noahhaworth/harry/src/champ/champ_description/meshes/arm/upper_arm.stl

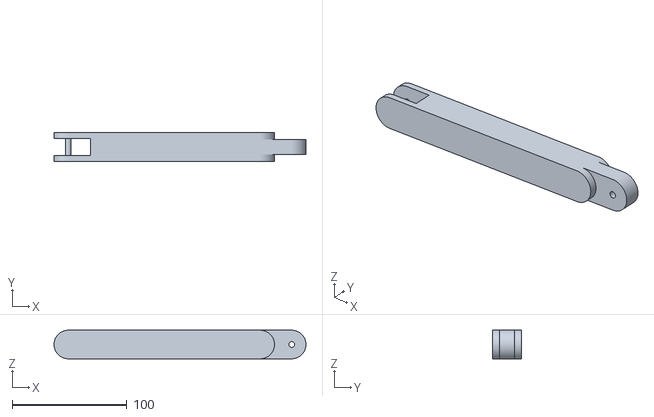
[picture p53: CAD file, 2022-01-09]
src/champ/champ_description/meshes/arm/upper_arm.stl
220.0 x 25.0 x 25.0
