noahhaworth/harry/src/champ/champ_description/meshes/base.stl

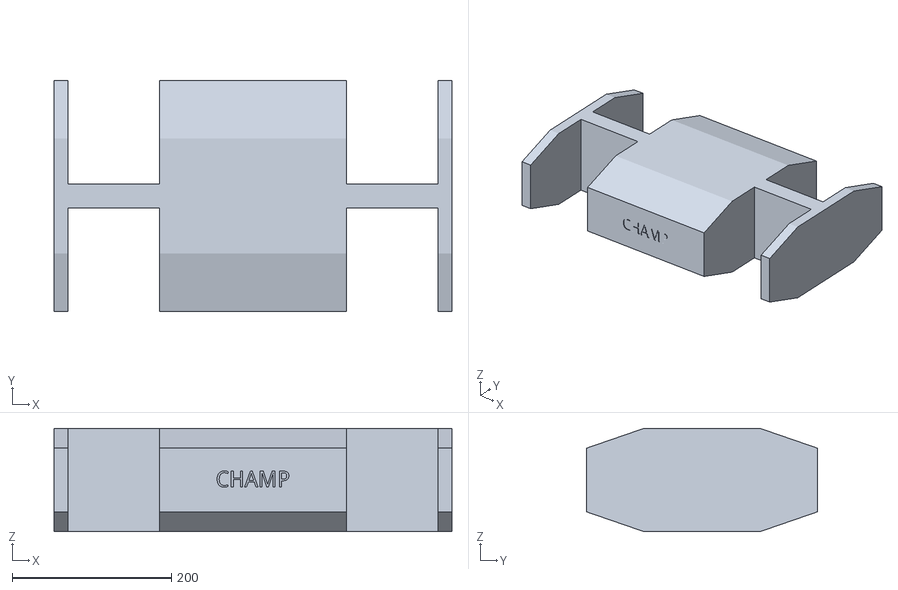
[picture p54: CAD file, 2022-01-09]
src/champ/champ_description/meshes/base.stl
500.0 x 290.0 x 130.0
