noahhaworth/harry/SolidWorks/servo.SLDPRT

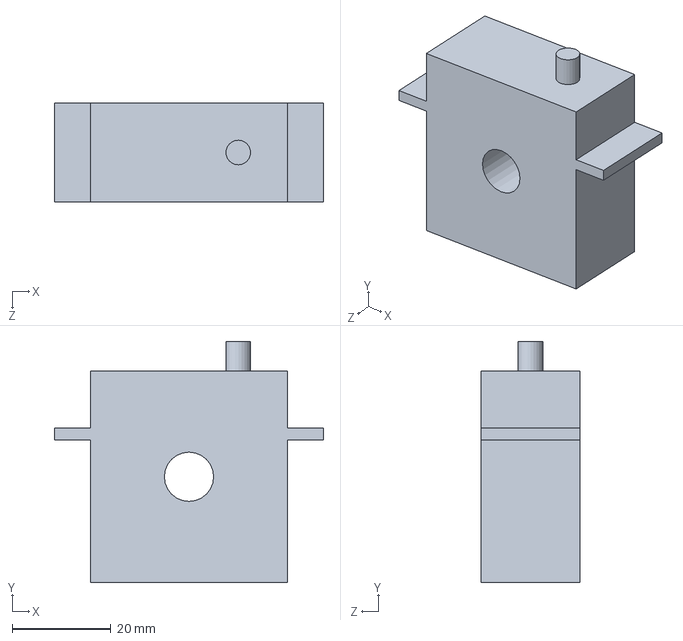
[picture p55: CAD file, 2022-05-04]
SolidWorks/servo.SLDPRT
54.6 x 49.0 x 20.0 mm
