noahhaworth/harry/src/champ/champ_description/meshes/arm/base.stl

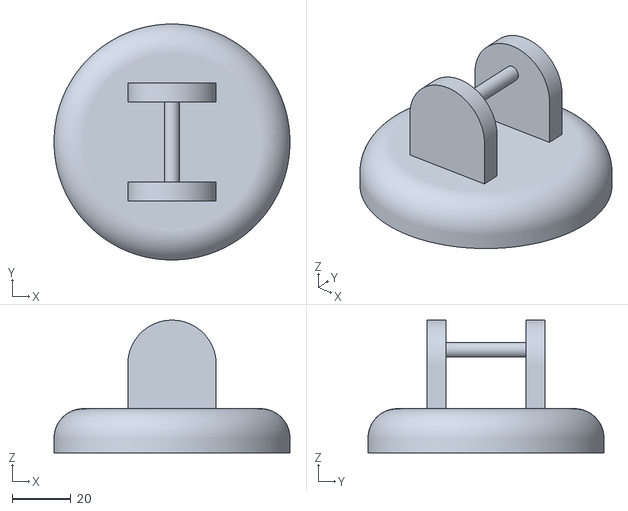
[picture p56: CAD file, 2022-01-09]
src/champ/champ_description/meshes/arm/base.stl
80.0 x 80.0 x 45.0
