noahhaworth/harry/SolidWorks/74_thread.SLDPRT

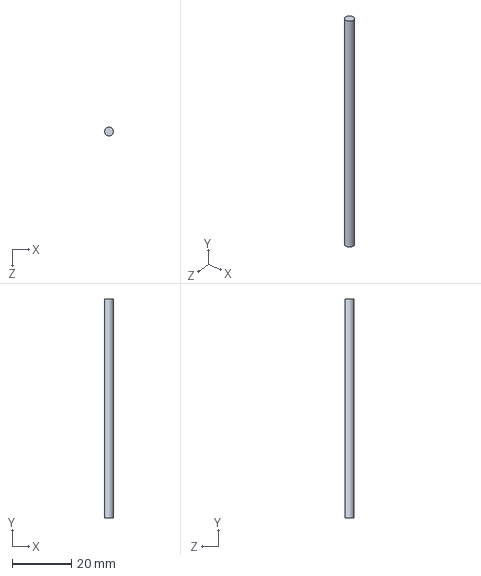
[picture p57: CAD file, 2022-05-04]
SolidWorks/74_thread.SLDPRT
3.00 x 74.0 x 3.00 mm
