noahhaworth/harry/SolidWorks/mlink2.SLDPRT

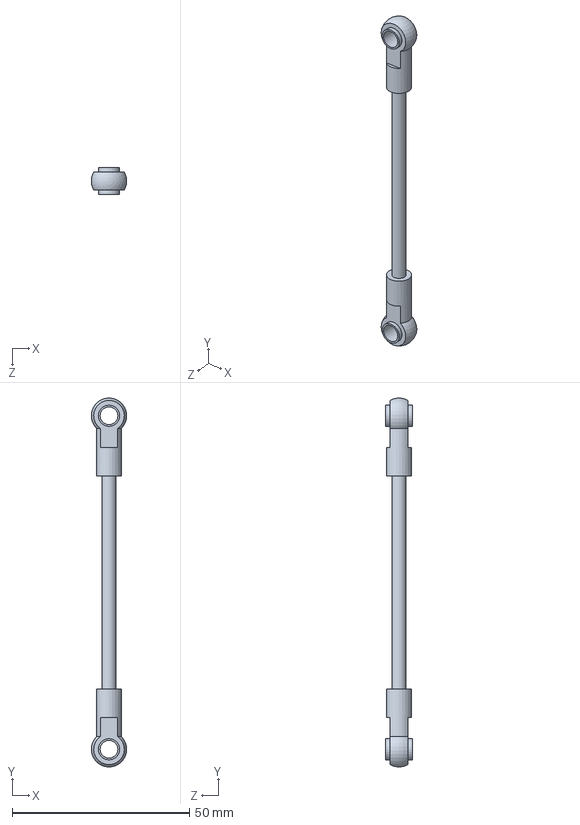
[picture p58: CAD file, 2022-05-04]
SolidWorks/mlink2.SLDPRT
9.98 x 104.0 x 7.50 mm
