noahhaworth/harry/SolidWorks/side_servo_mount.SLDPRT

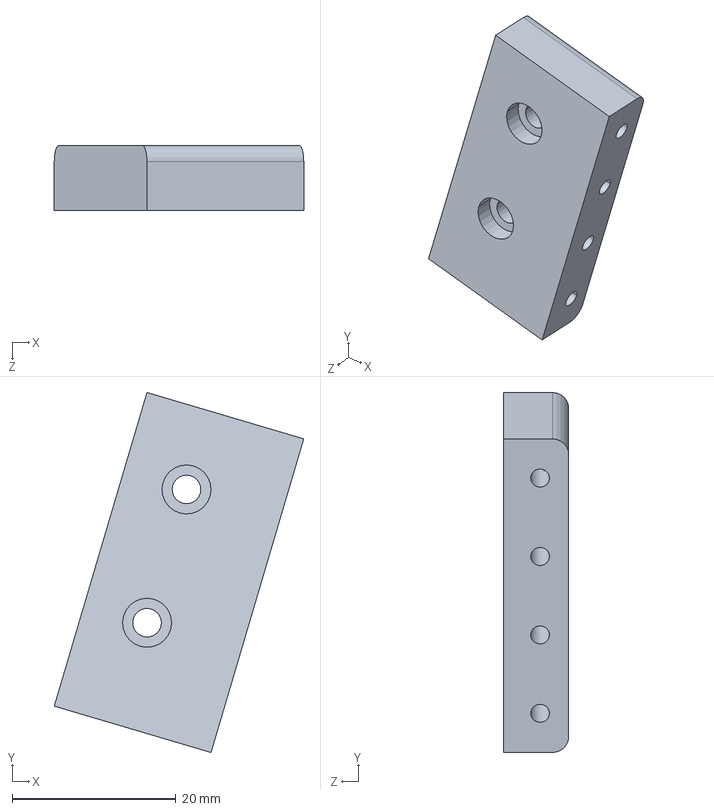
[picture p59: CAD file, 2022-05-04]
SolidWorks/side_servo_mount.SLDPRT
30.5 x 44.0 x 8.00 mm
