noahhaworth/harry/SolidWorks/lowerleg_l.SLDPRT

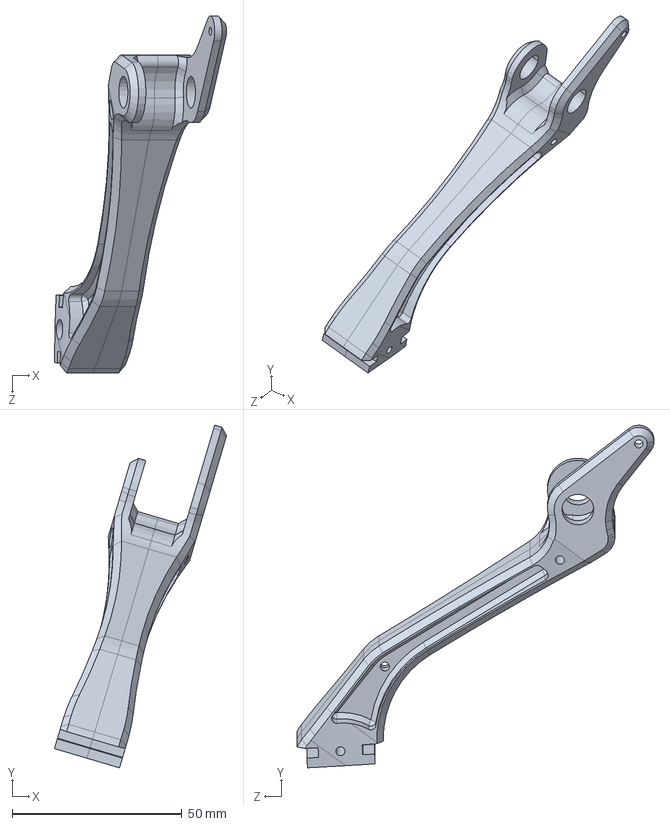
[picture p60: CAD file, 2022-05-04]
SolidWorks/lowerleg_l.SLDPRT
50.7 x 101.0 x 105.2 mm
