noahhaworth/harry/SolidWorks/Servo MG996R.SLDPRT

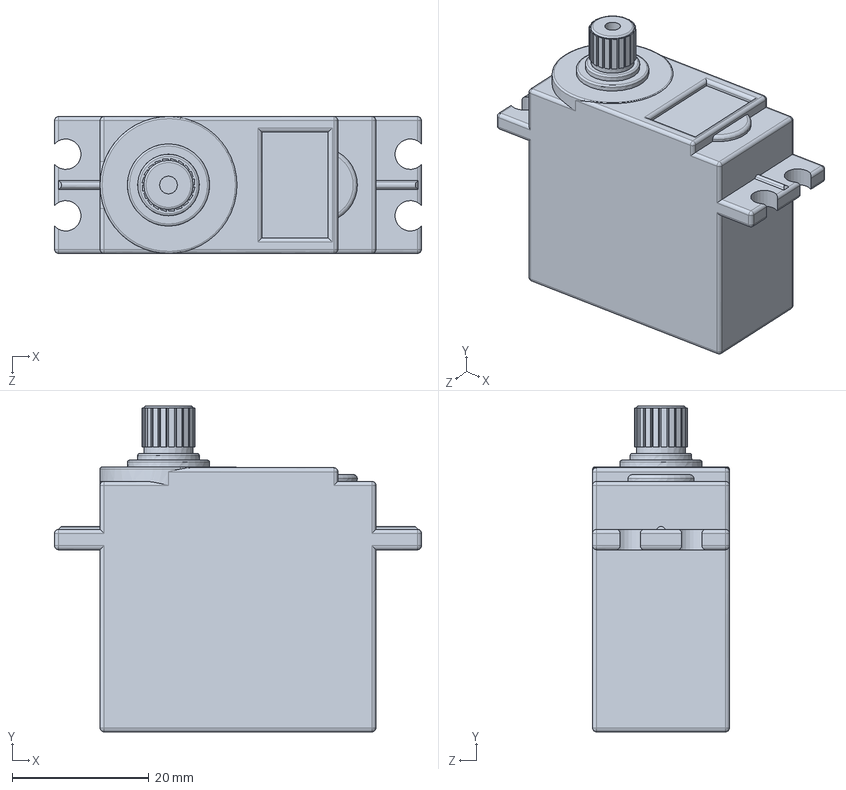
[picture p61: CAD file, 2022-05-04]
SolidWorks/Servo MG996R.SLDPRT
53.6 x 47.6 x 20.0 mm
