noahhaworth/harry/SolidWorks/upperleg.SLDPRT

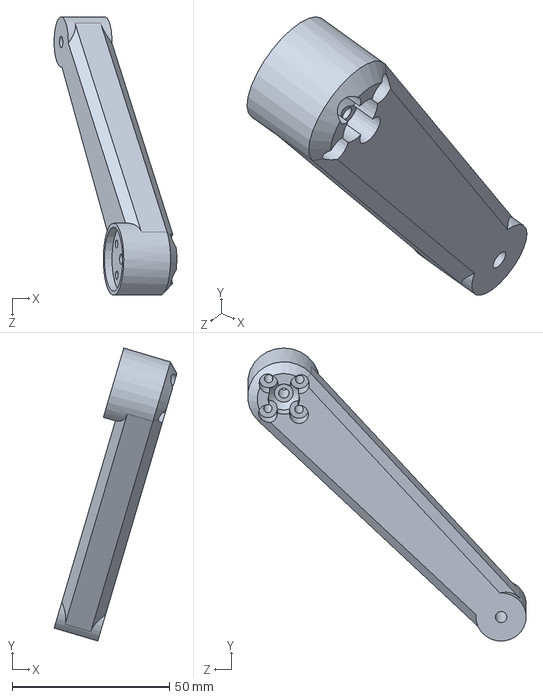
[picture p62: CAD file, 2022-05-04]
SolidWorks/upperleg.SLDPRT
39.1 x 93.2 x 88.5 mm
