noahhaworth/harry/SolidWorks/mlink1.SLDPRT

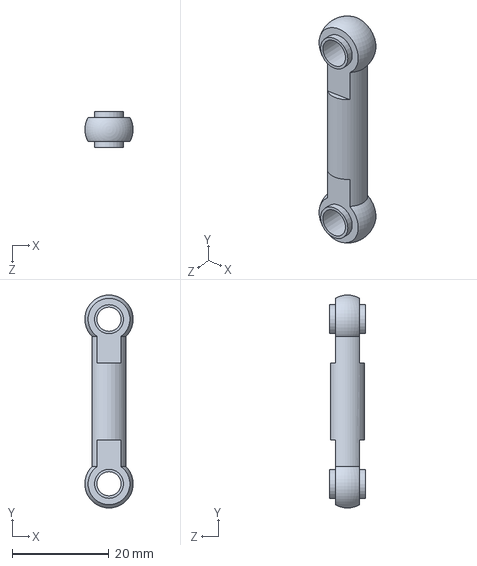
[picture p63: CAD file, 2022-05-04]
SolidWorks/mlink1.SLDPRT
9.98 x 44.0 x 7.50 mm
