noahhaworth/harry/SolidWorks/foot.SLDPRT

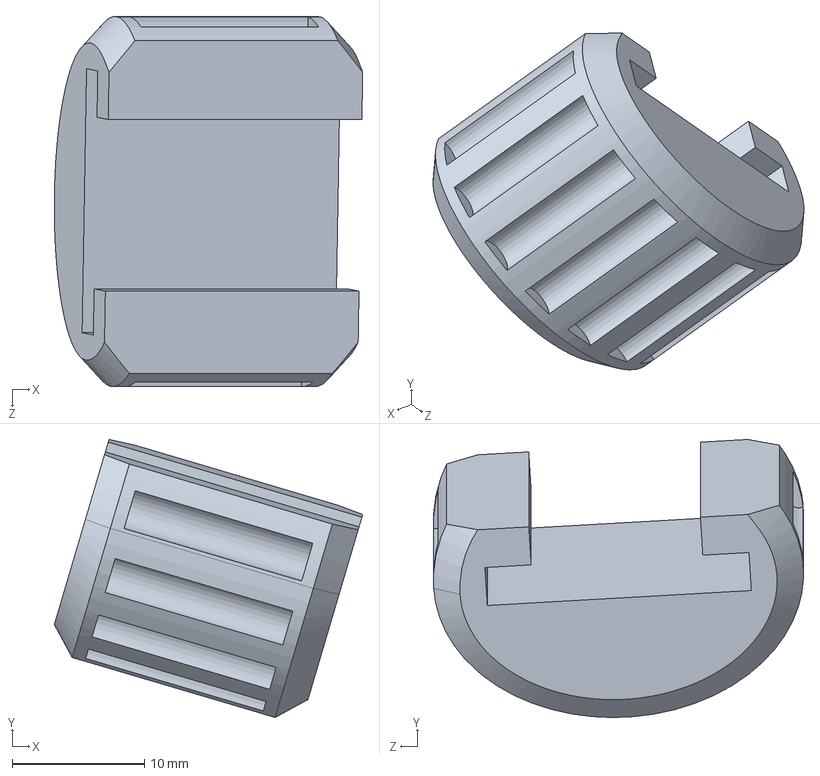
[picture p64: CAD file, 2022-05-04]
SolidWorks/foot.SLDPRT
23.3 x 21.0 x 28.0 mm
