noahhaworth/harry/SolidWorks/pi.SLDPRT

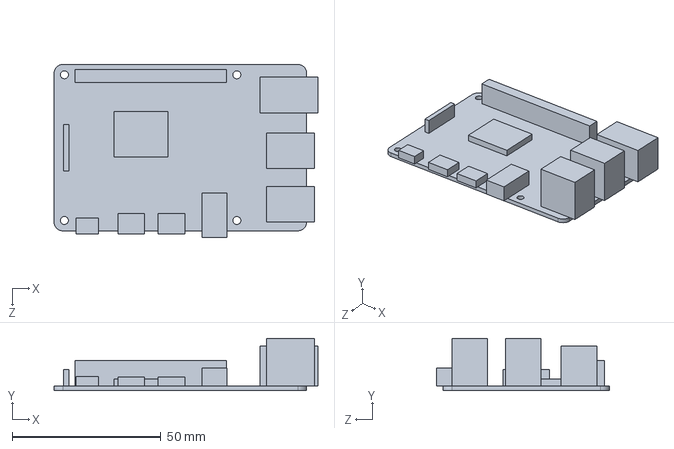
[picture p65: CAD file, 2022-05-04]
SolidWorks/pi.SLDPRT
88.8 x 17.6 x 58.2 mm
