noahhaworth/harry/SolidWorks/link3_m.SLDPRT

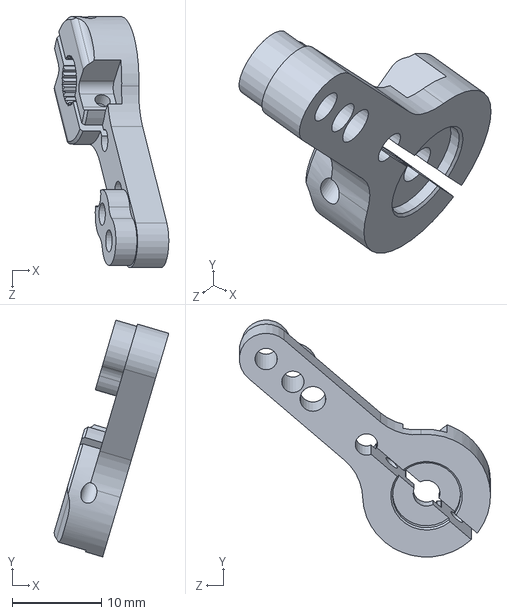
[picture p66: CAD file, 2022-05-04]
SolidWorks/link3_m.SLDPRT
12.8 x 26.5 x 28.1 mm
