noahhaworth/harry/SolidWorks/joint_r.SLDPRT

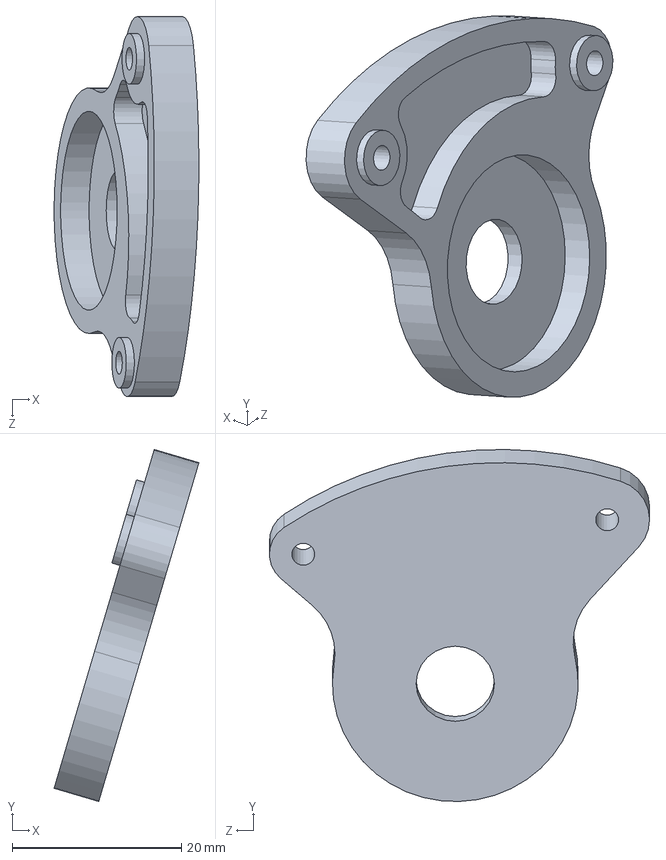
[picture p67: CAD file, 2022-05-04]
SolidWorks/joint_r.SLDPRT
17.1 x 41.5 x 44.9 mm
