noahhaworth/harry/SolidWorks/ball_joint.SLDPRT

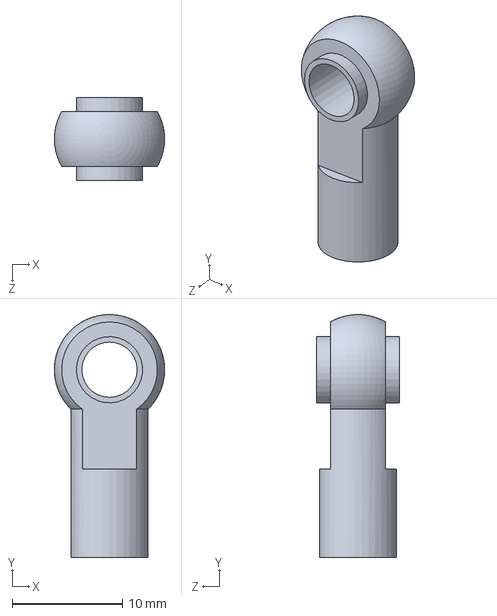
[picture p68: CAD file, 2022-05-04]
SolidWorks/ball_joint.SLDPRT
9.99 x 22.0 x 7.50 mm
