noahhaworth/harry/SolidWorks/Part2.SLDPRT

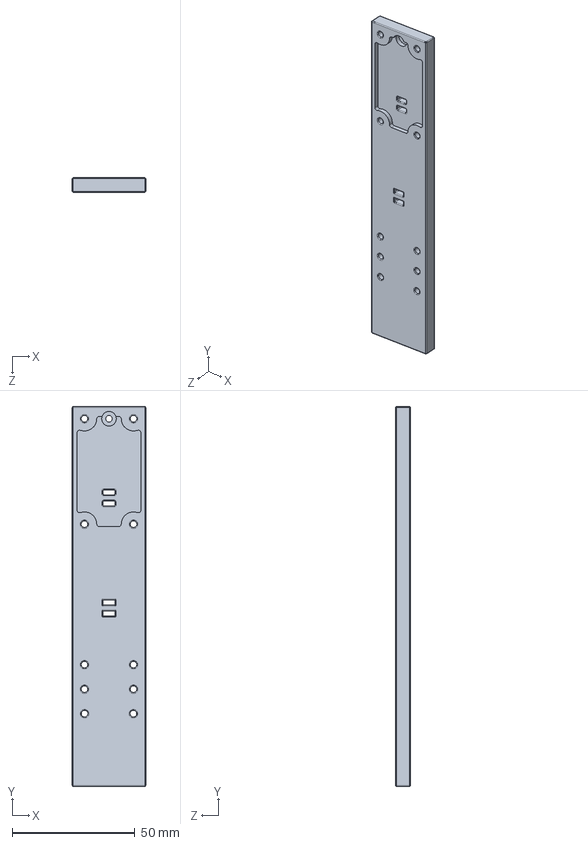
[picture p69: CAD file, 2022-05-04]
SolidWorks/Part2.SLDPRT
30.0 x 155.0 x 6.00 mm
