noahhaworth/harry/SolidWorks/n_servo_siding.SLDPRT

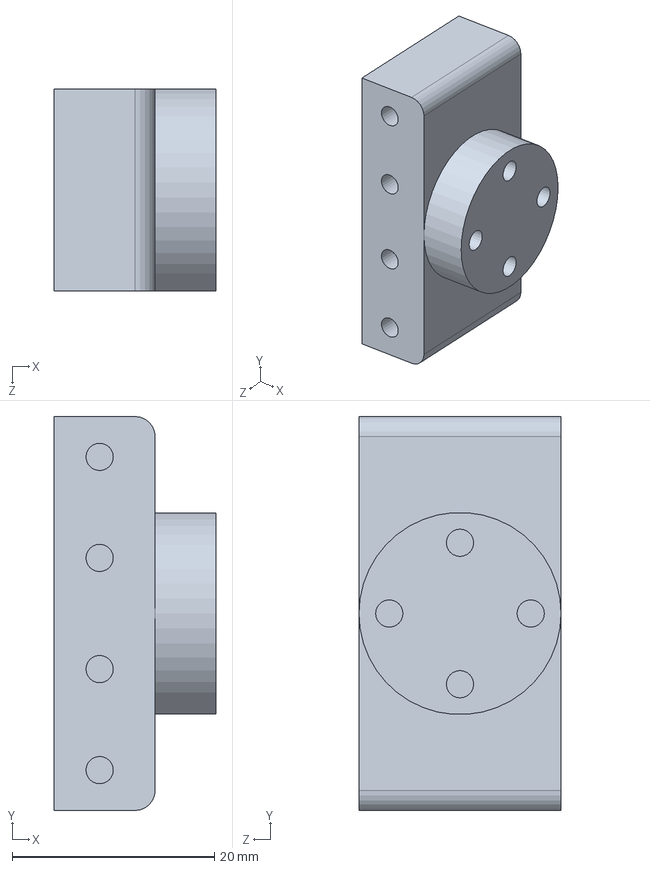
[picture p70: CAD file, 2022-05-04]
SolidWorks/n_servo_siding.SLDPRT
16.0 x 39.0 x 20.0 mm
