noahhaworth/harry/SolidWorks/link_joint.SLDPRT

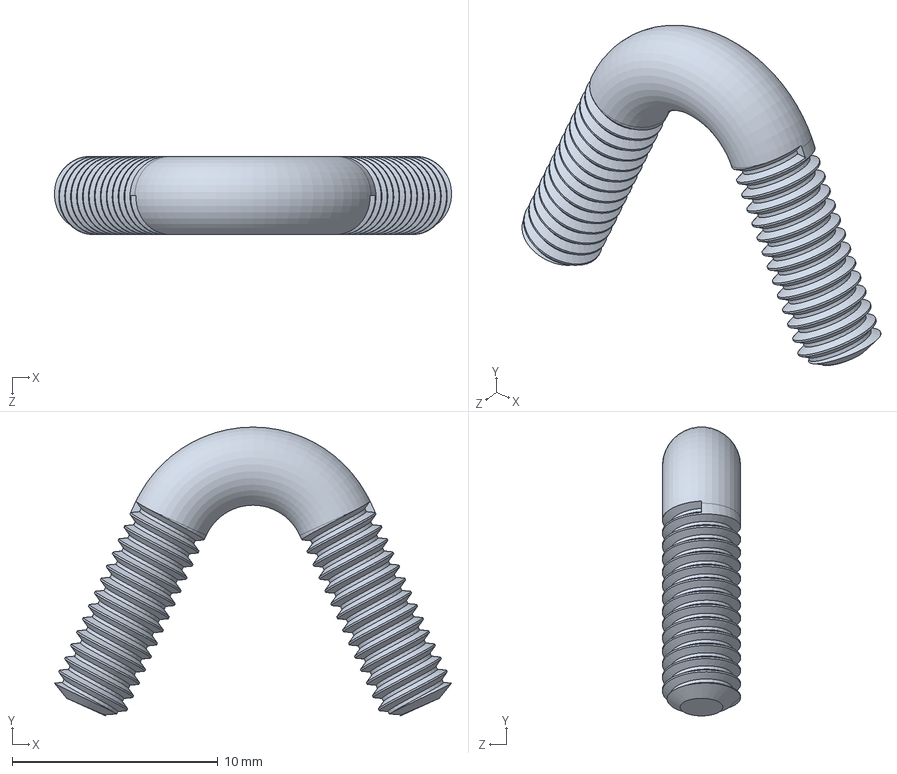
[picture p71: CAD file, 2022-05-04]
SolidWorks/link_joint.SLDPRT
19.3 x 14.0 x 3.80 mm
