noahhaworth/harry/SolidWorks/joint_l.SLDPRT

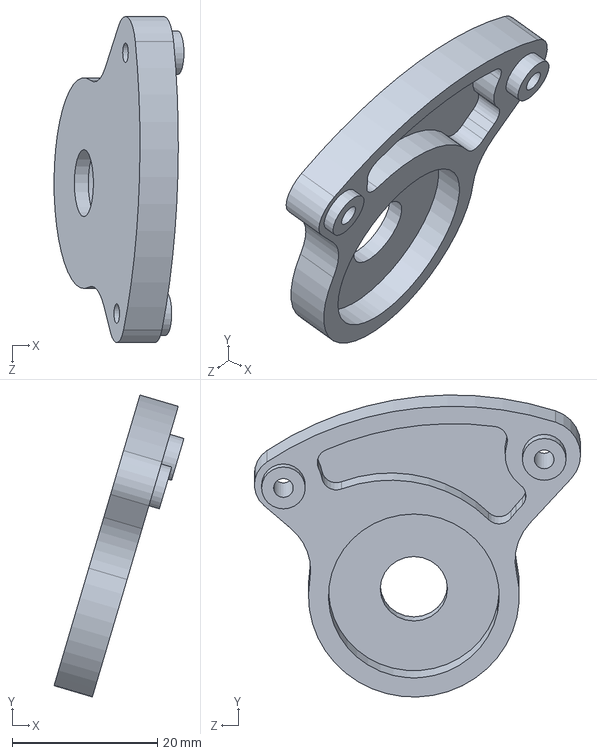
[picture p72: CAD file, 2022-05-04]
SolidWorks/joint_l.SLDPRT
17.9 x 41.5 x 44.9 mm
