noahhaworth/harry/SolidWorks/threads.SLDPRT

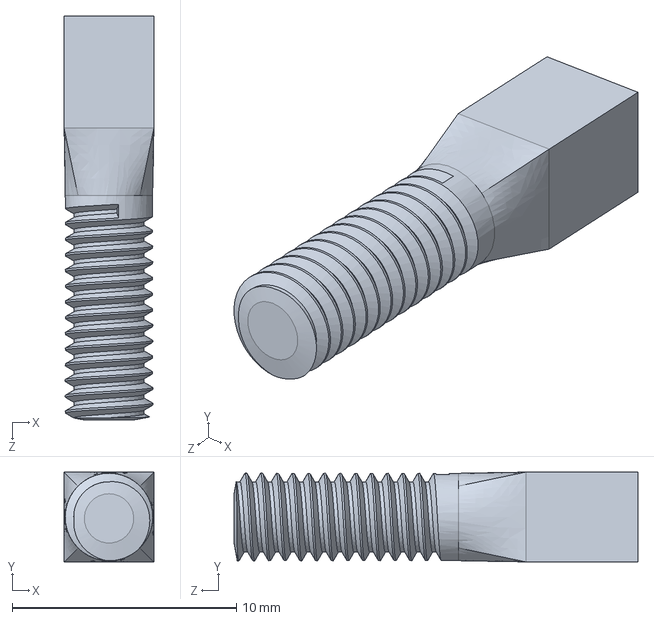
[picture p73: CAD file, 2022-05-04]
SolidWorks/threads.SLDPRT
4.00 x 4.00 x 18.0 mm
