noahhaworth/harry/SolidWorks/my_2order.SLDPRT

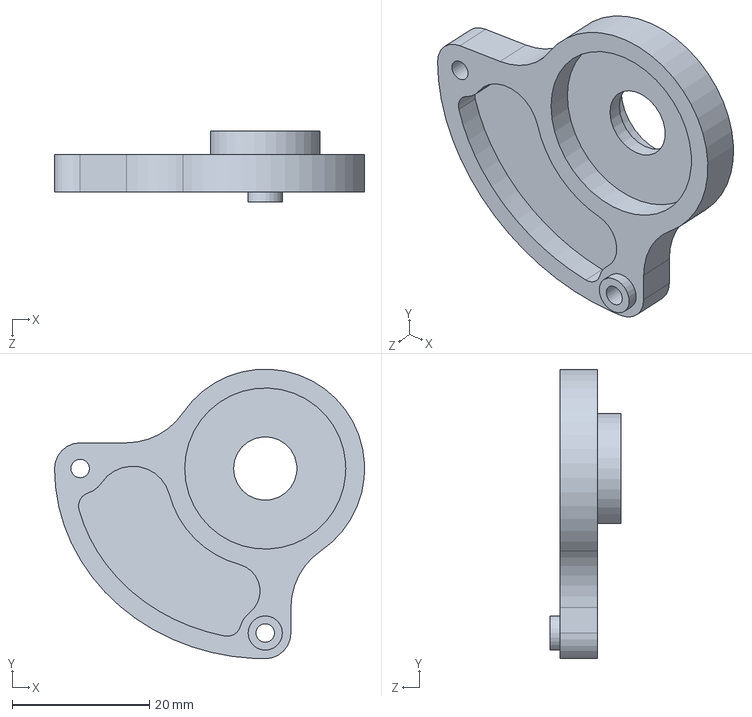
[picture p74: CAD file, 2022-05-04]
SolidWorks/my_2order.SLDPRT
45.2 x 42.2 x 10.4 mm
