noahhaworth/harry/SolidWorks/link2_m.SLDPRT

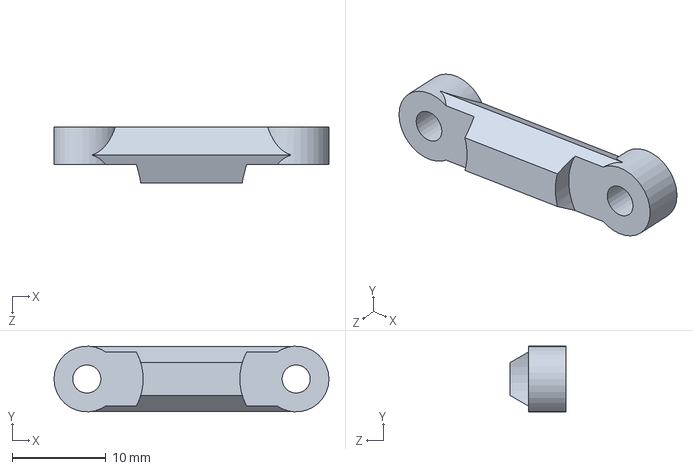
[picture p75: CAD file, 2022-05-04]
SolidWorks/link2_m.SLDPRT
29.3 x 6.99 x 6.00 mm
