noahhaworth/harry/SolidWorks/m_servo_siding.SLDPRT

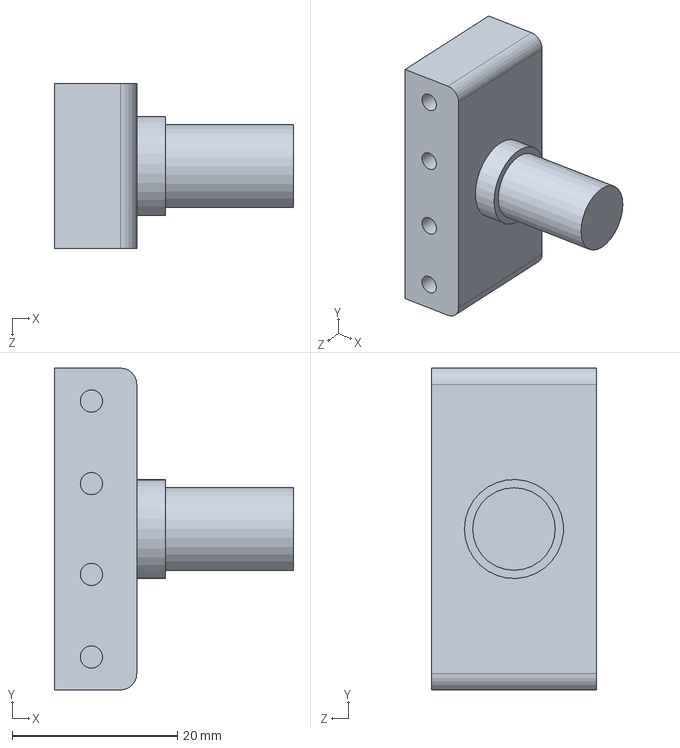
[picture p76: CAD file, 2022-05-04]
SolidWorks/m_servo_siding.SLDPRT
29.0 x 39.0 x 20.0 mm
