noahhaworth/harry/SolidWorks/Part1.SLDPRT

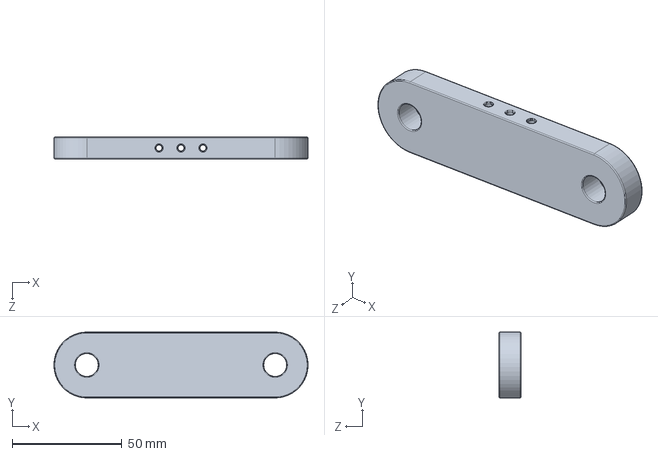
[picture p77: CAD file, 2022-05-04]
SolidWorks/Part1.SLDPRT
115.8 x 30.0 x 10.0 mm
