noahhaworth/harry/SolidWorks/circular_horn.SLDPRT

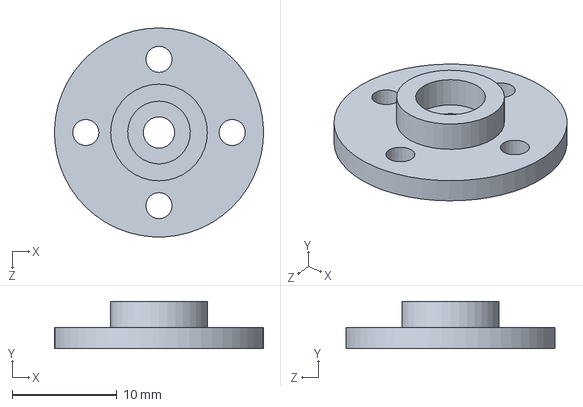
[picture p78: CAD file, 2022-05-04]
SolidWorks/circular_horn.SLDPRT
20.0 x 4.50 x 20.0 mm
