noahhaworth/harry/SolidWorks/holder.SLDPRT

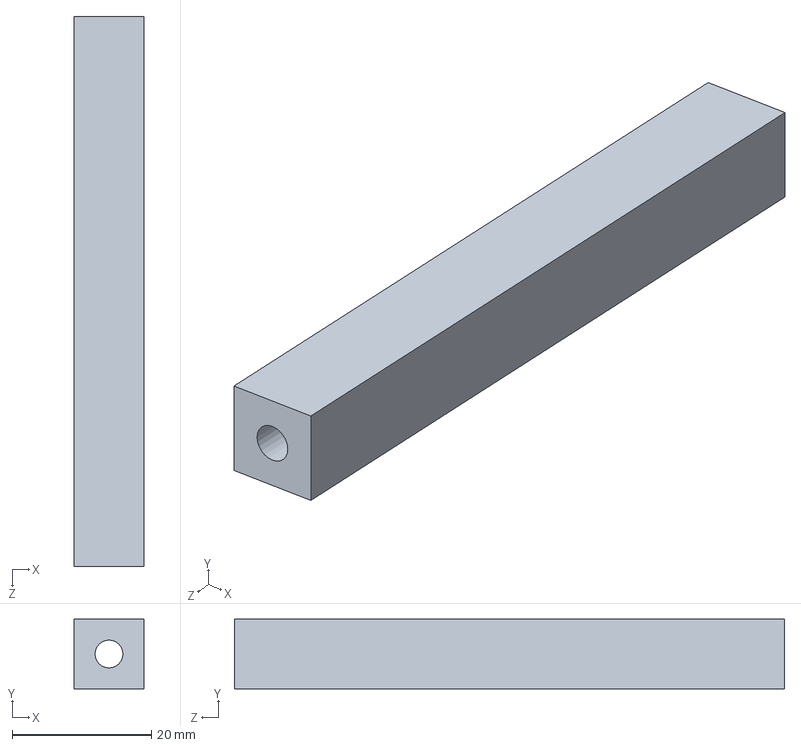
[picture p79: CAD file, 2022-05-04]
SolidWorks/holder.SLDPRT
10.0 x 10.0 x 79.0 mm
